wilyarti/weather_station/3D_files/insert.stl

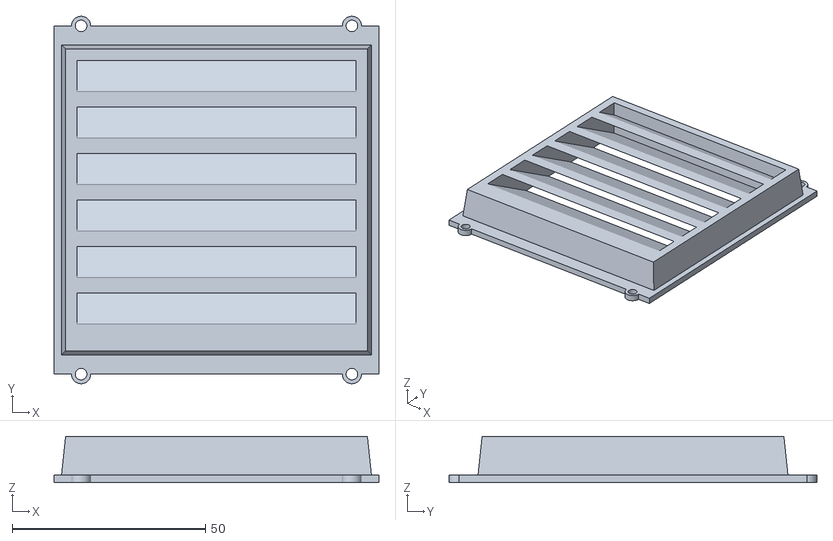
[picture p11: CAD file, 2018-12-13]
3D_files/insert.stl
84.0 x 95.0 x 12.0
