wilyarti/weather_station/Weather_Station_Project/solar_panel_side_clip.stl

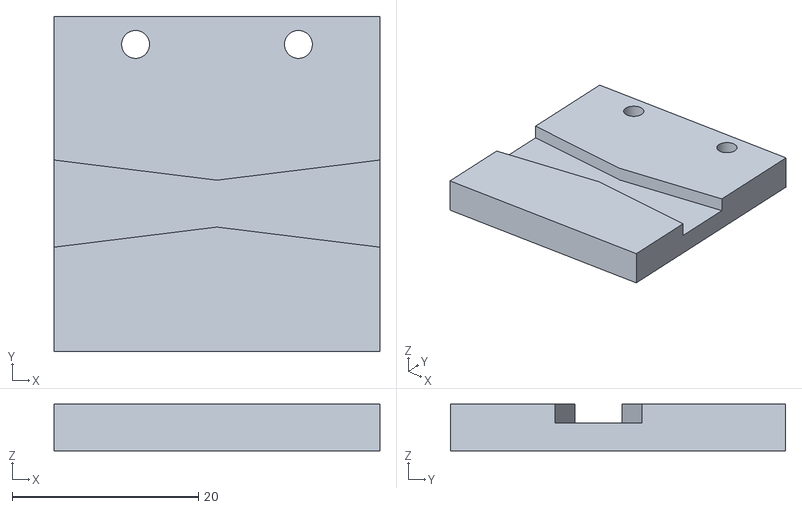
[picture p12: CAD file, 2019-05-02]
Weather_Station_Project/solar_panel_side_clip.stl
35.0 x 36.0 x 5.00
