wilyarti/weather_station/3D_files/roof_foldable.stl

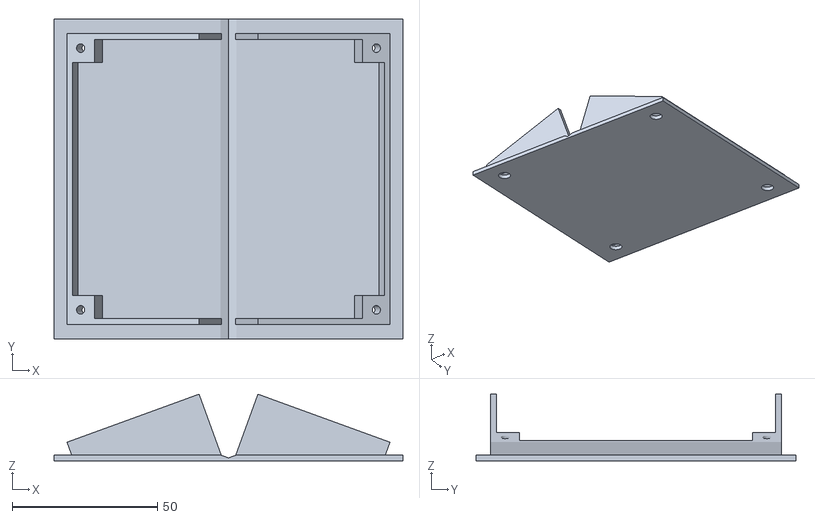
[picture p13: CAD file, 2018-12-13]
3D_files/roof_foldable.stl
120.0 x 110.0 x 22.9
