wilyarti/weather_station/Weather_Station_Project/cone_pattern.stl

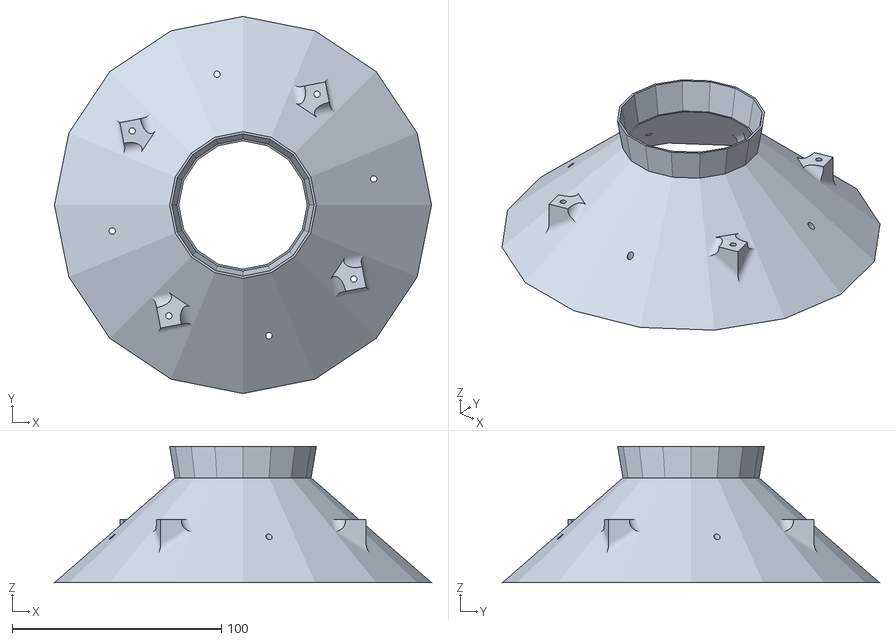
[picture p14: CAD file, 2019-05-02]
Weather_Station_Project/cone_pattern.stl
180.0 x 180.0 x 65.0
