wilyarti/weather_station/3D_files/base.stl

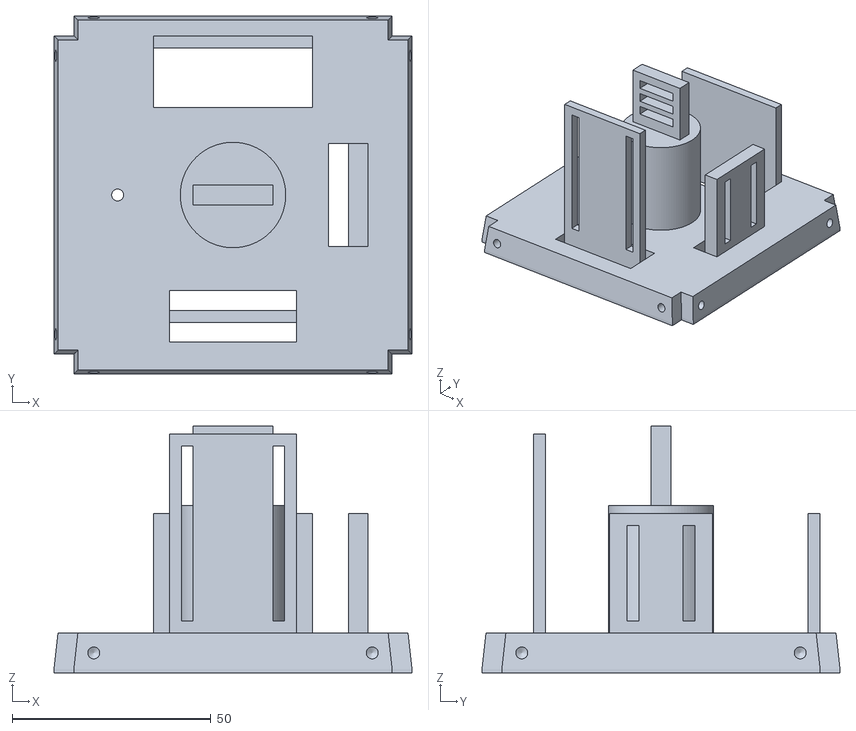
[picture p15: CAD file, 2018-12-13]
3D_files/base.stl
90.0 x 90.0 x 62.0
