wilyarti/weather_station/Weather_Station_Project/boxbase_solar_esp8285.stl

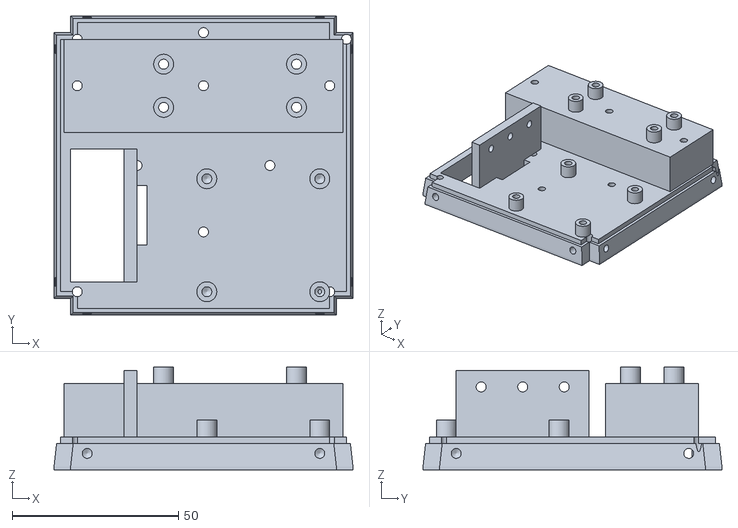
[picture p16: CAD file, 2019-05-02]
Weather_Station_Project/boxbase_solar_esp8285.stl
90.0 x 90.0 x 31.0
