wilyarti/weather_station/3D_files/truss.stl

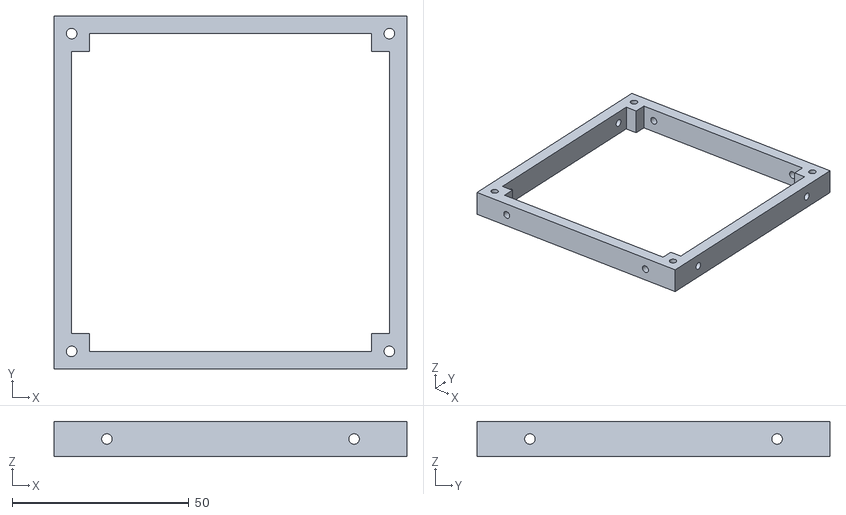
[picture p17: CAD file, 2018-12-13]
3D_files/truss.stl
100.0 x 100.0 x 10.0
