wilyarti/weather_station/Weather_Station_Project/electronics_cover.stl

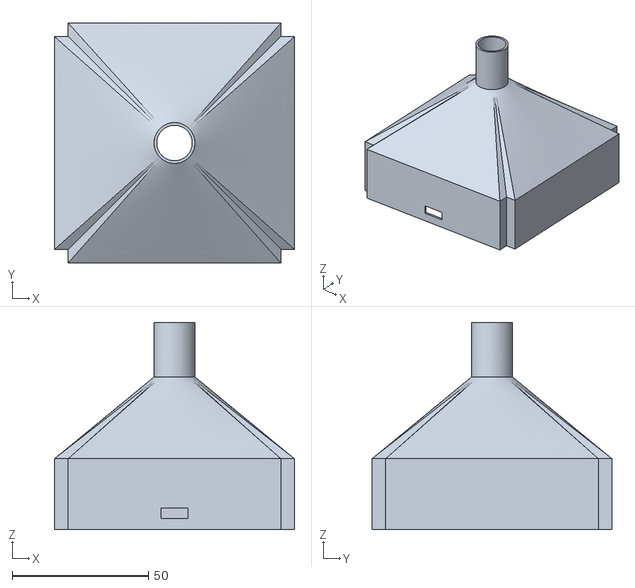
[picture p18: CAD file, 2019-05-02]
Weather_Station_Project/electronics_cover.stl
88.0 x 88.0 x 76.0
