wilyarti/weather_station/Weather_Station_Project/uv_sensor_base.stl

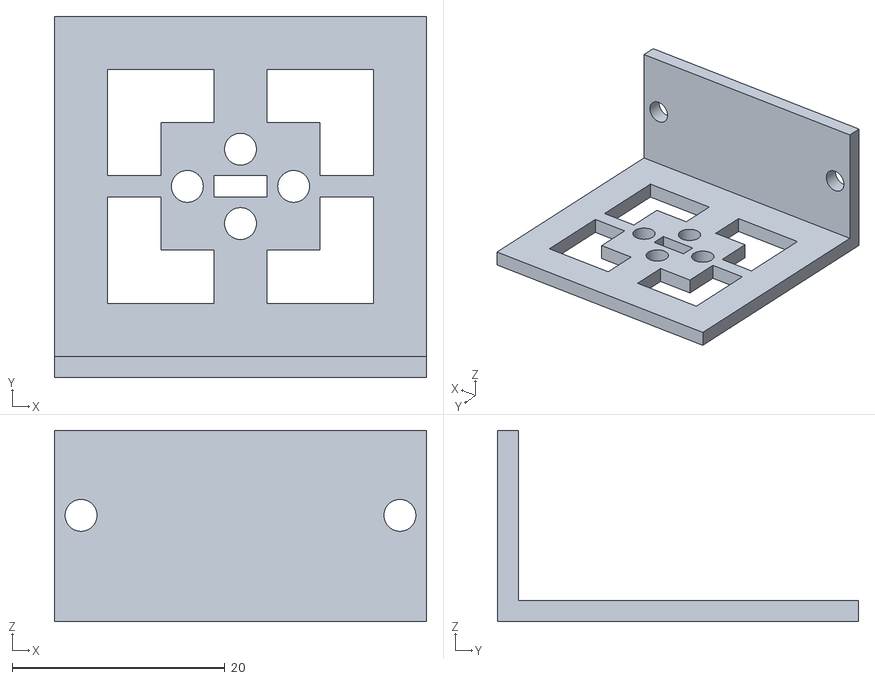
[picture p19: CAD file, 2019-05-02]
Weather_Station_Project/uv_sensor_base.stl
35.0 x 34.0 x 18.0
